Archive-663/lensAdapters/Olympus PEN-F/ASSETS/dumbAdapter_DKL_PENF (1).jpg

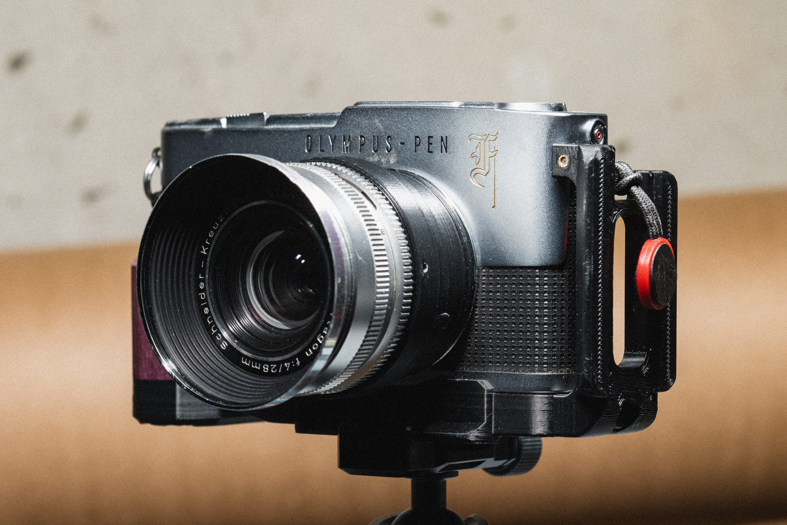
Olympus PEN-F/ASSETS/dumbAdapter_DKL_PENF (1).jpg
