Archive-663/lensAdapters/Olympus PEN-F/ASSETS/dumbAdapter_PENF.jpg

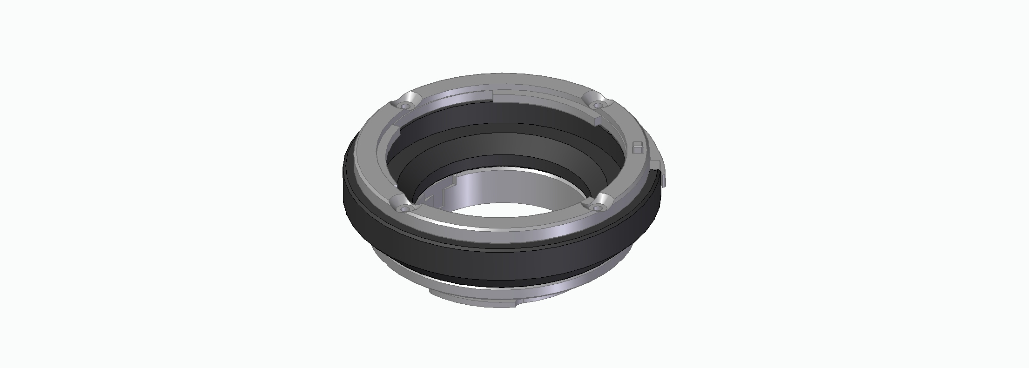
Olympus PEN-F/ASSETS/dumbAdapter_PENF.jpg
