Archive-663/lensAdapters/Olympus PEN-F/SHIFT/M42/ASSETS/productShift_M43_PENF (1).jpg

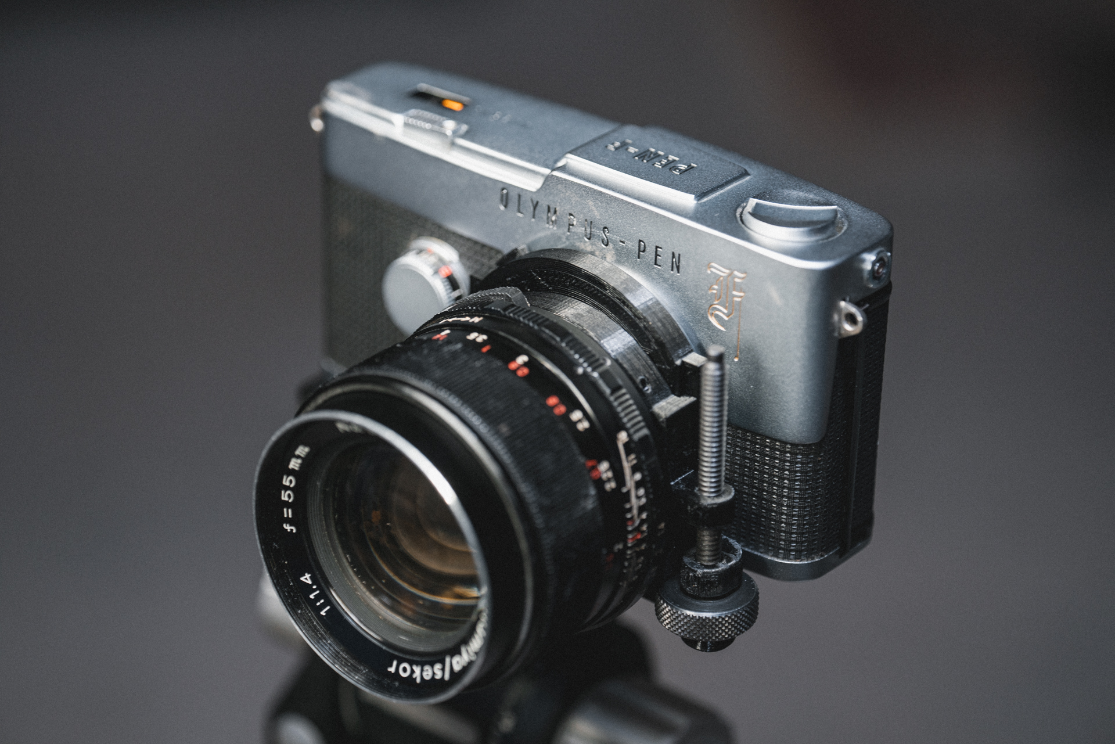
Olympus PEN-F/SHIFT/M42/ASSETS/productShift_M43_PENF (1).jpg
