Archive-663/lensAdapters/Olympus PEN-F/SHIFT/M42/ASSETS/productShift_M43_PENF (9).jpg

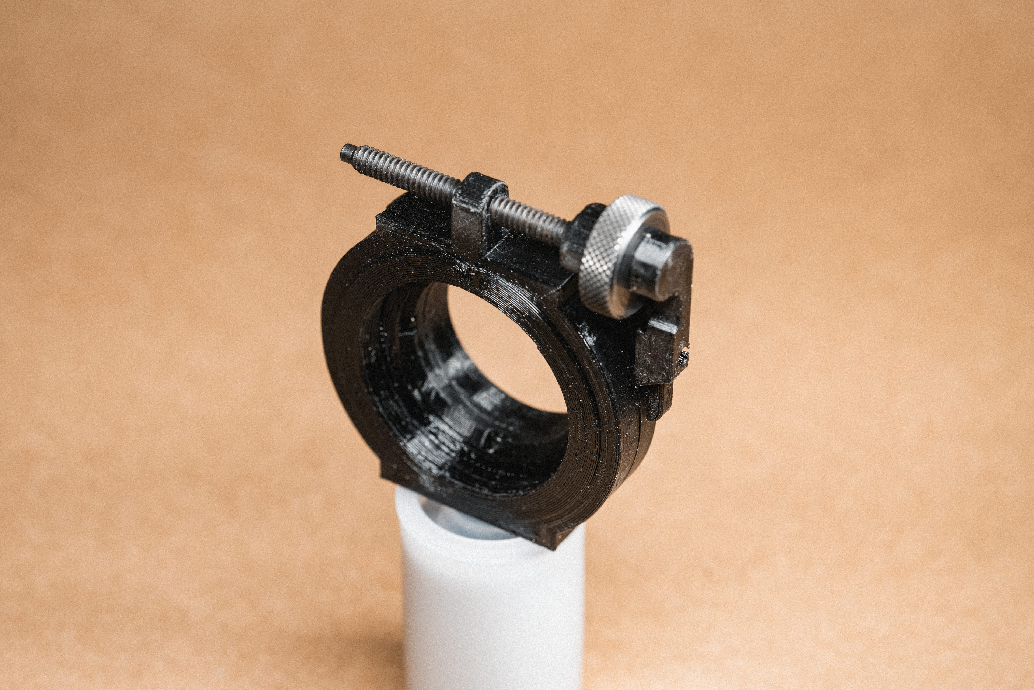
Olympus PEN-F/SHIFT/M42/ASSETS/productShift_M43_PENF (9).jpg
