Archive-663/lensAdapters/Olympus PEN-F/SHIFT/Nikon F/ASSETS/productShift_NIKF_PENF (7).jpg

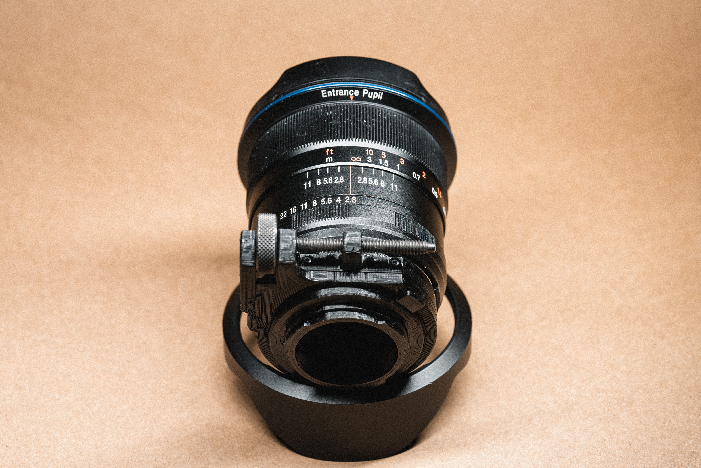
Olympus PEN-F/SHIFT/Nikon F/ASSETS/productShift_NIKF_PENF (7).jpg
