Archive-663/lensAdapters/Olympus PEN-F/SPEEDBOOSTER/Mamiya 645/ASSETS/productSB_M645_PENF (6).jpg

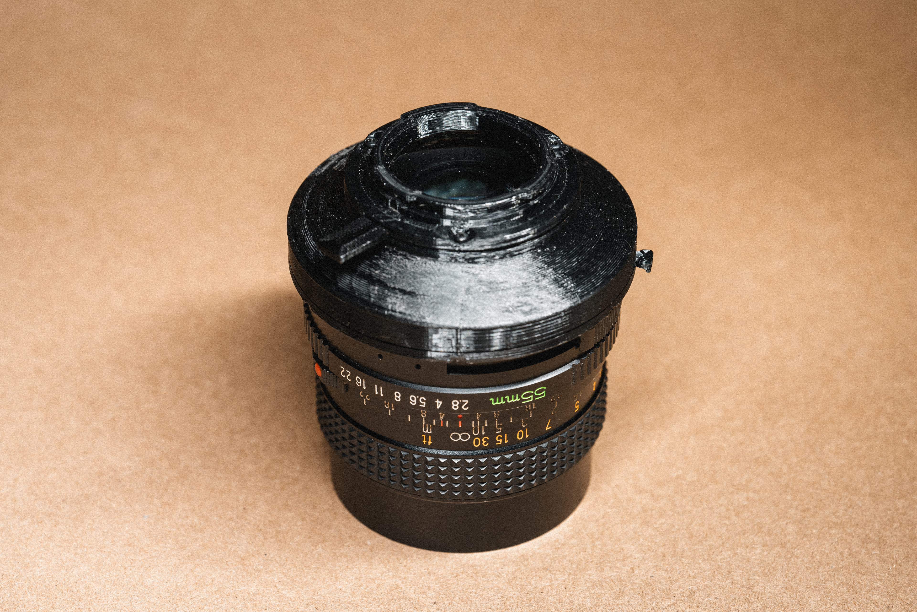
Olympus PEN-F/SPEEDBOOSTER/Mamiya 645/ASSETS/productSB_M645_PENF (6).jpg
