Archive-663/lensAdapters/Olympus PEN-F/DUMB/Canon FD/STEP/dumbBody_CFD_PENF.stp

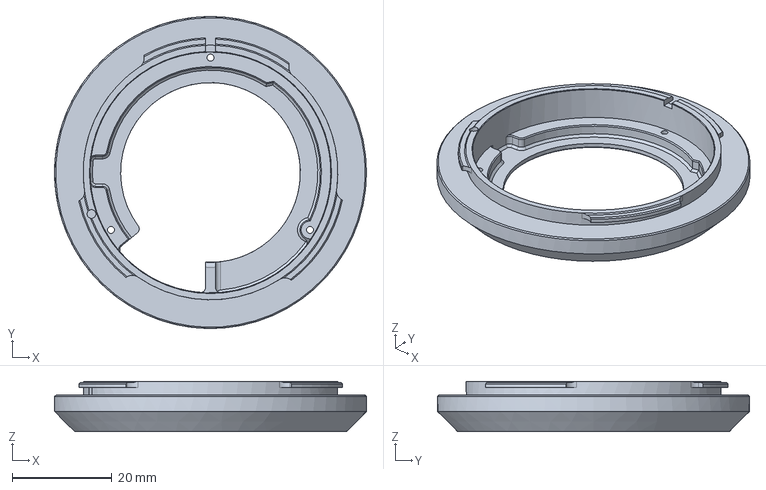
[picture p47: CAD file, 2025-03-07]
Olympus PEN-F/DUMB/Canon FD/STEP/dumbBody_CFD_PENF.stp
62.5 x 62.5 x 10.1 mm
