Archive-663/lensAdapters/Olympus PEN-F/DUMB/Canon FD/STL/dumbBody_CFD_PENF_printOrientation.3mf

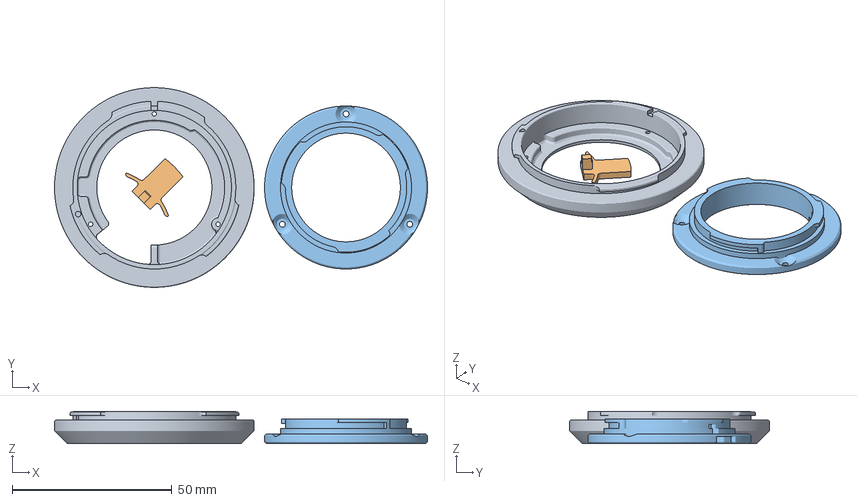
[picture p48: CAD file, 2025-03-07]
Olympus PEN-F/DUMB/Canon FD/STL/dumbBody_CFD_PENF_printOrientation.3mf
116.7 x 62.5 x 10.1 mm
dumbBody_CFD_PENF.stl
mountLensBase_lensLock_extended_PENF.stl
mountLensDumbBody_CFD_PENF.stl
