Archive-663/lensAdapters/Olympus PEN-F/DUMB/DKL/STL/mountBodyApertureRing_DKL_stepless.stl

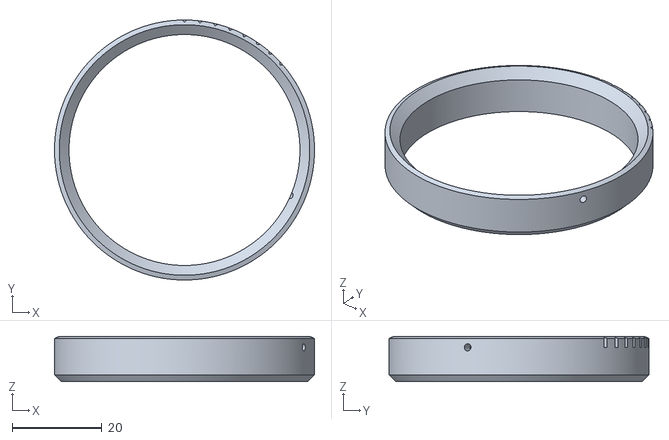
[picture p49: CAD file, 2023-10-16]
Olympus PEN-F/DUMB/DKL/STL/mountBodyApertureRing_DKL_stepless.stl
58.0 x 58.0 x 10.1
