Archive-663/lensAdapters/Olympus PEN-F/DUMB/M42/STL/printOrientation_baseDumbBody_M42_PENF.3mf

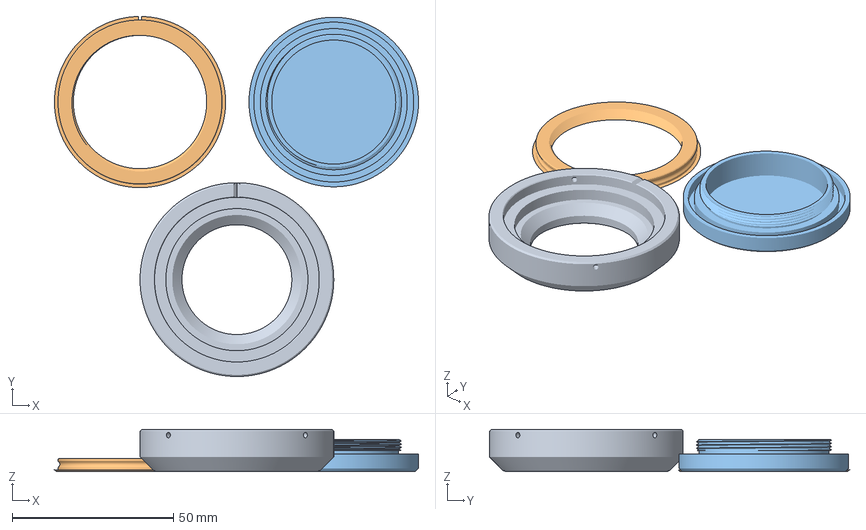
[picture p50: CAD file, 2023-09-29]
Olympus PEN-F/DUMB/M42/STL/printOrientation_baseDumbBody_M42_PENF.3mf
112.7 x 111.5 x 13.1 mm
dumbBody_M42_PENF.stl
mountBodyBaseThread_M42_PENF.stl
baseBodyCap_M42.stl
