Archive-663/lensAdapters/Olympus PEN-F/DUMB/mountDumbBase_PENF/STEP/mountLensLock_PENF.stp

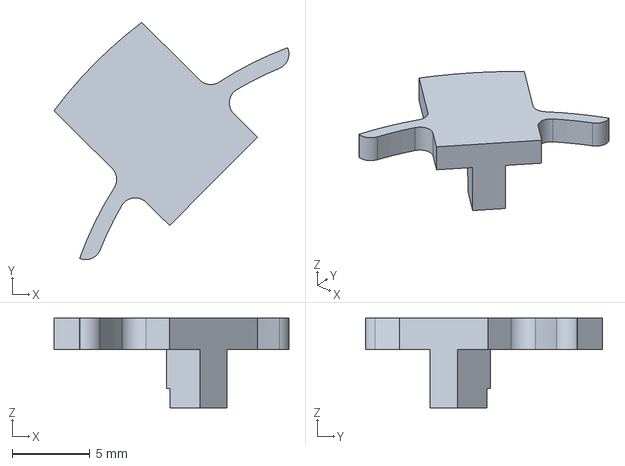
[picture p51: CAD file, 2023-09-29]
Olympus PEN-F/DUMB/mountDumbBase_PENF/STEP/mountLensLock_PENF.stp
15.1 x 15.2 x 5.75 mm
