Archive-663/lensAdapters/Olympus PEN-F/DUMB/mountDumbBase_PENF/STL/printOrientation_baseDumb_PENF.3mf

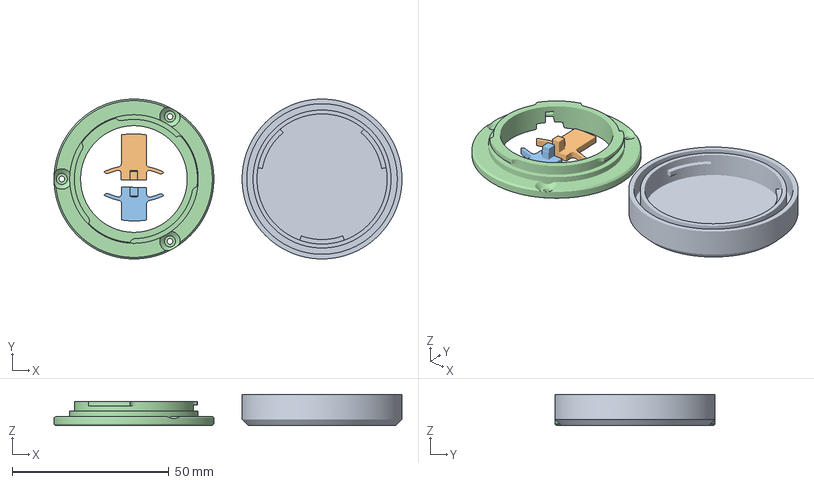
[picture p52: CAD file, 2023-09-29]
Olympus PEN-F/DUMB/mountDumbBase_PENF/STL/printOrientation_baseDumb_PENF.3mf
111.0 x 51.0 x 10.0 mm
baseRearCap_PENF.stl
mountLensLock_Extended_PENF.stl
mountLensLock_PENF.stl
mountLensBase_PENF.stl
