Archive-663/lensAdapters/Olympus PEN-F/DUMB/Nikon F/STL/printOrientation_baseDumbBody_NIKF_PENF.3mf

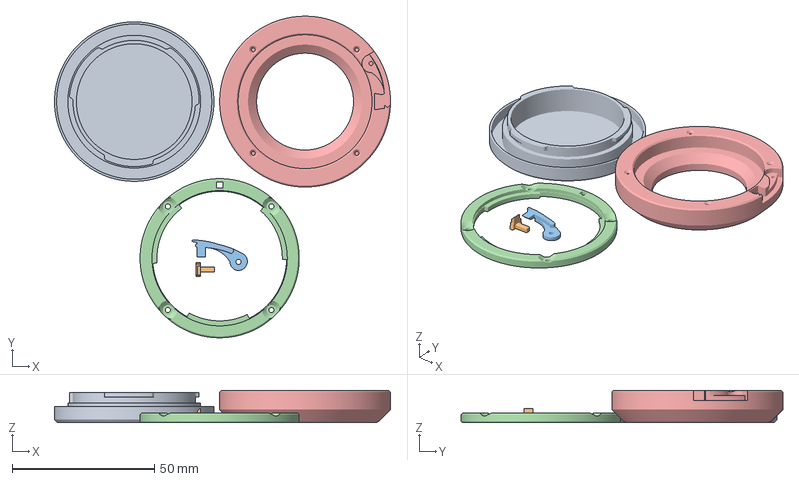
[picture p53: CAD file, 2023-09-29]
Olympus PEN-F/DUMB/Nikon F/STL/printOrientation_baseDumbBody_NIKF_PENF.3mf
118.0 x 112.9 x 11.3 mm
baseBodyCap_NIKF.stl
mountBodyPin_NIKF.stl
mountBodyPinLock_NIKF.stl
mountBodyBase_NIKF.stl
dumbBody_NIKF_PENF.stl
