Archive-663/lensAdapters/Olympus PEN-F/DUMB/Olympus OM/STL/dumbBody_OM_PENF_printOrientation.3mf

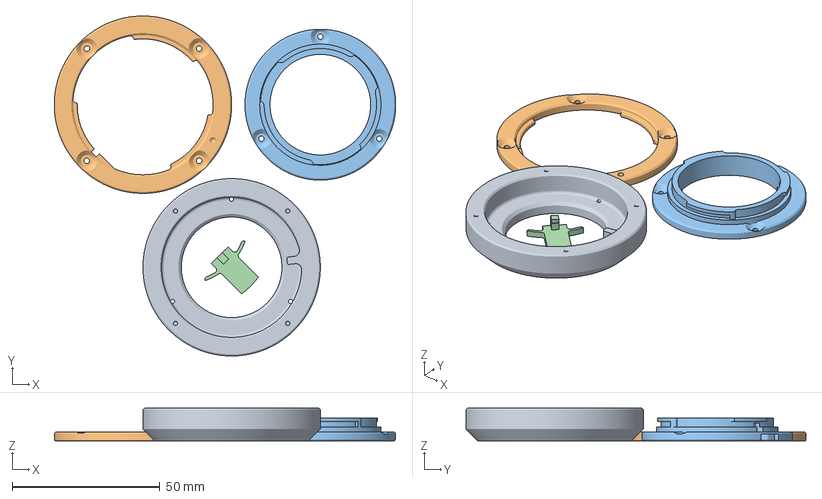
[picture p54: CAD file, 2025-08-07]
Olympus PEN-F/DUMB/Olympus OM/STL/dumbBody_OM_PENF_printOrientation.3mf
115.5 x 115.0 x 11.1 mm
dumbBody_OM_PENF.stl
dumbBodyFlange_OM_PENF.stl
mountLensDumbBody_PENF.stl
mountLensLock_Extended_PENF.stl
