Archive-663/lensAdapters/Olympus PEN-F/SHIFT/M42/STL/printOrientation_baseShiftBody_M42_PENF.3mf

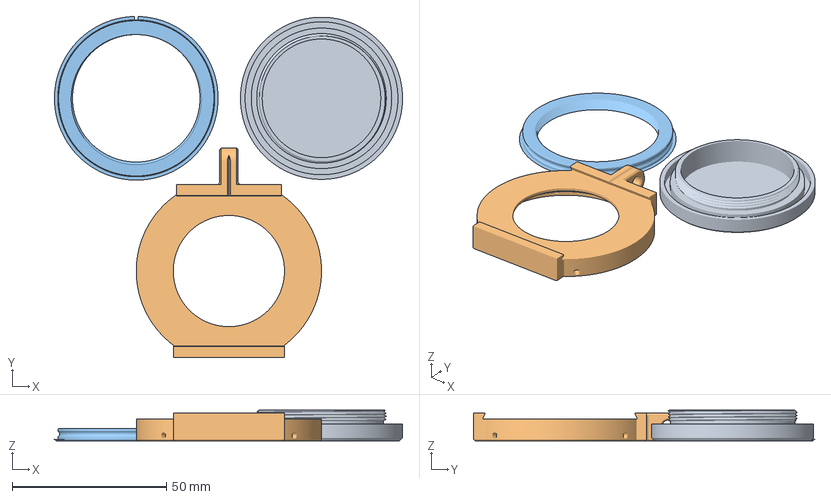
[picture p55: CAD file, 2023-09-29]
Olympus PEN-F/SHIFT/M42/STL/printOrientation_baseShiftBody_M42_PENF.3mf
112.7 x 110.4 x 10.0 mm
baseBodyCap_M42.stl
shiftTopPlate_M42_PENF.stl
mountBodyBaseThread_M42.stl
