Archive-663/lensAdapters/Olympus PEN-F/SHIFT/mountShiftBase_PENF/STL/printOrientation_baseShift_PENF.3mf

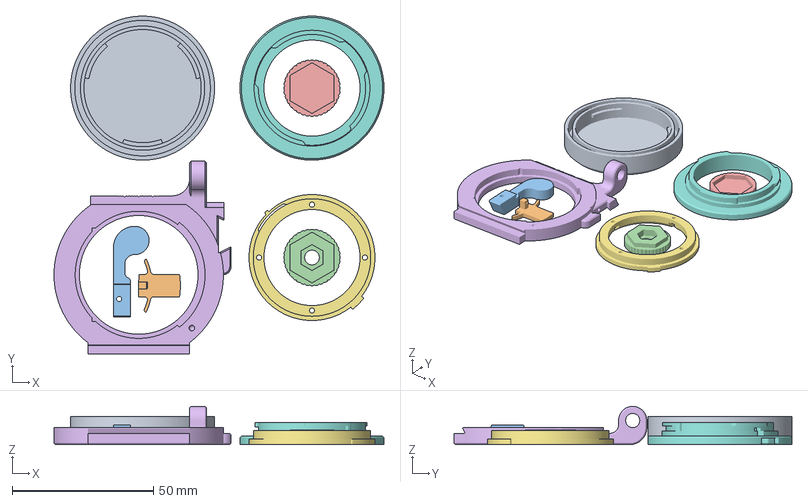
[picture p56: CAD file, 2023-09-29]
Olympus PEN-F/SHIFT/mountShiftBase_PENF/STL/printOrientation_baseShift_PENF.3mf
116.9 x 119.6 x 13.5 mm
baseRearCap_PENF.stl
shiftBaseMountLock_Extended_PENF.stl
shiftBaseBottomPlate_screwCap_PENF.stl
shiftBaseScrewCap_Bottom_PENF.stl
shiftBaseScrewCap_Top_PENF.stl
shiftBaseBottomPlate_PENF.stl
shiftBaseRotator_PENF.stl
shiftBaseMount_PENF.stl
