Archive-663/lensAdapters/Olympus PEN-F/SHIFT/Nikon F/STL/printOrientation_baseShiftBody_NIKF_PENF.3mf

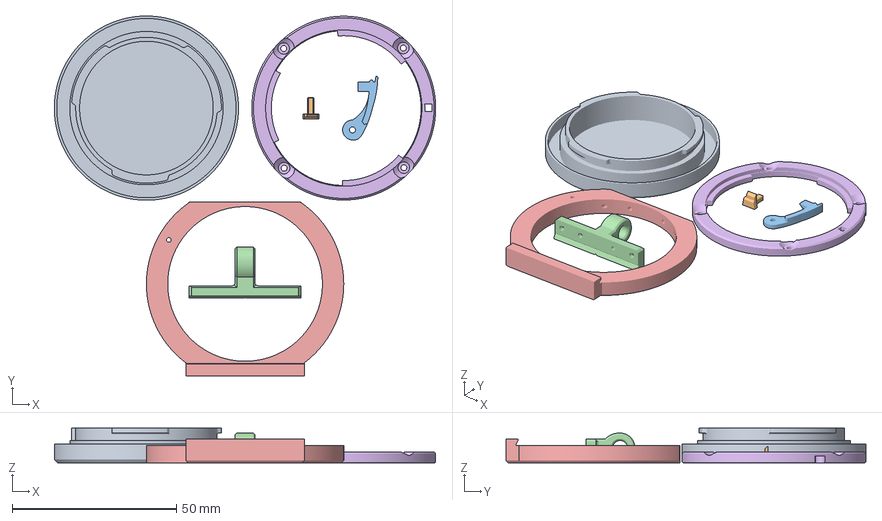
[picture p57: CAD file, 2023-09-29]
Olympus PEN-F/SHIFT/Nikon F/STL/printOrientation_baseShiftBody_NIKF_PENF.3mf
115.9 x 109.4 x 10.5 mm
baseBodyCap_NIKF.stl
mountBodyPin_NIKF.stl
mountBodyPinLock_NIKF.stl
shiftTopPlateShift_NIKF_PENF.stl
shiftTopPlate_NIKF_PENF.stl
mountBodyBase_NIKF.stl
