Archive-663/lensAdapters/Olympus PEN-F/SPEEDBOOSTER/Mamiya 645/STL/printOrientation_speedBooster_M645_PENF.3mf

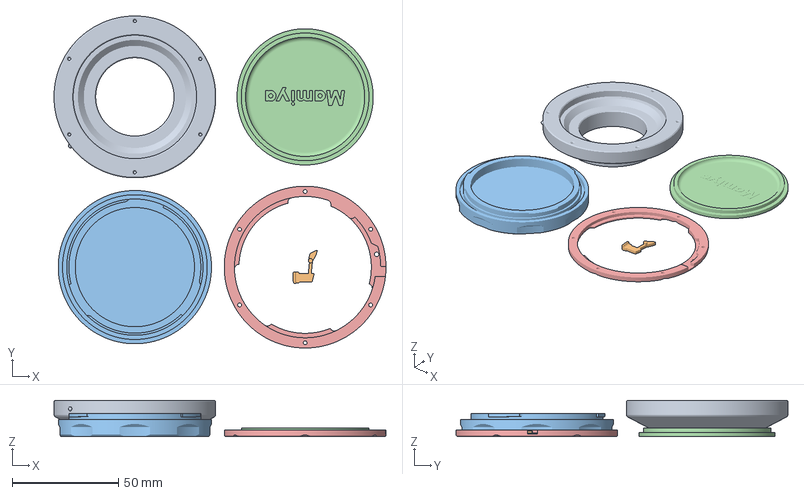
[picture p58: CAD file, 2023-09-29]
Olympus PEN-F/SPEEDBOOSTER/Mamiya 645/STL/printOrientation_speedBooster_M645_PENF.3mf
156.0 x 156.0 x 17.0 mm
speedBoosterBody_M645_PENF.stl
mountBodyLock_M645.stl
baseBodyCap_M645.stl
baseBodyCap_faceplate_M645.stl
mountBodyBase_M645.stl
