Archive-663/lensAdapters/Olympus PEN-F/SPEEDBOOSTER/mountSpeedBoosterBase_PENF/STEP/mountLensLock_Extended_PENF.stp

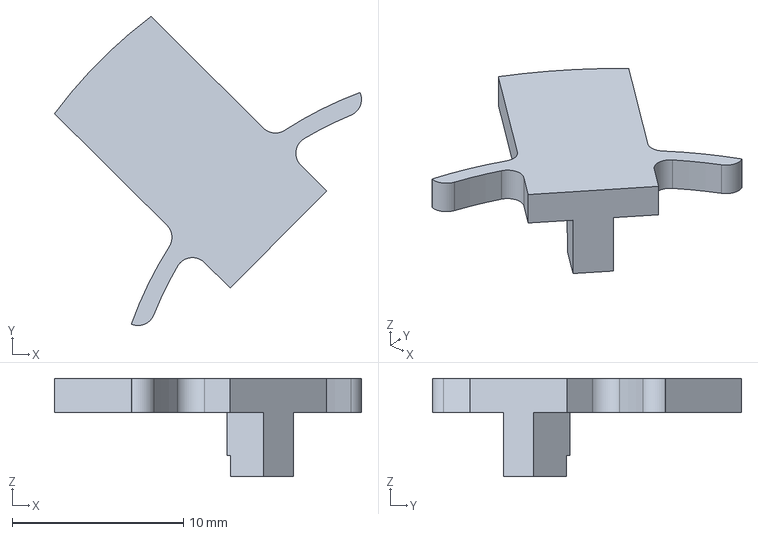
[picture p59: CAD file, 2023-09-29]
Olympus PEN-F/SPEEDBOOSTER/mountSpeedBoosterBase_PENF/STEP/mountLensLock_Extended_PENF.stp
17.9 x 18.1 x 5.75 mm
