Archive-663/lensAdapters/Canon EF-Mount/STEP/M42-EF EF Mount Body.step

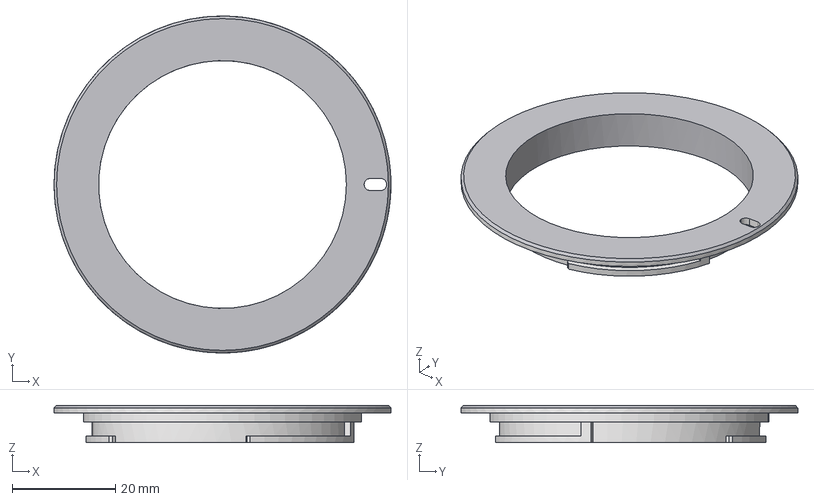
[picture p60: CAD file, 2023-06-25]
Canon EF-Mount/STEP/M42-EF EF Mount Body.step
65.3 x 65.3 x 7.21 mm
