Archive-663/lensAdapters/Fuji GFX/DUMB/Bronica S2/STEP/mountBodyBase_flange_BS_GFX.stp

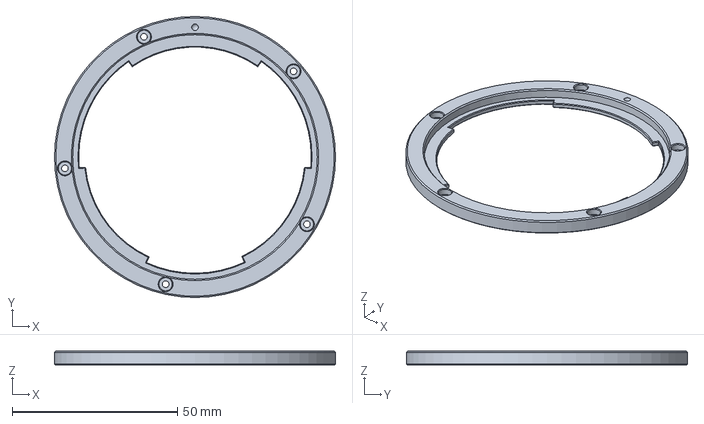
[picture p61: CAD file, 2026-01-14]
Fuji GFX/DUMB/Bronica S2/STEP/mountBodyBase_flange_BS_GFX.stp
85.0 x 85.0 x 4.25 mm
