Archive-663/lensAdapters/Fuji GFX/DUMB/Bronica S2/STL/dumbBody_BS_GFX_printOrientation.3mf

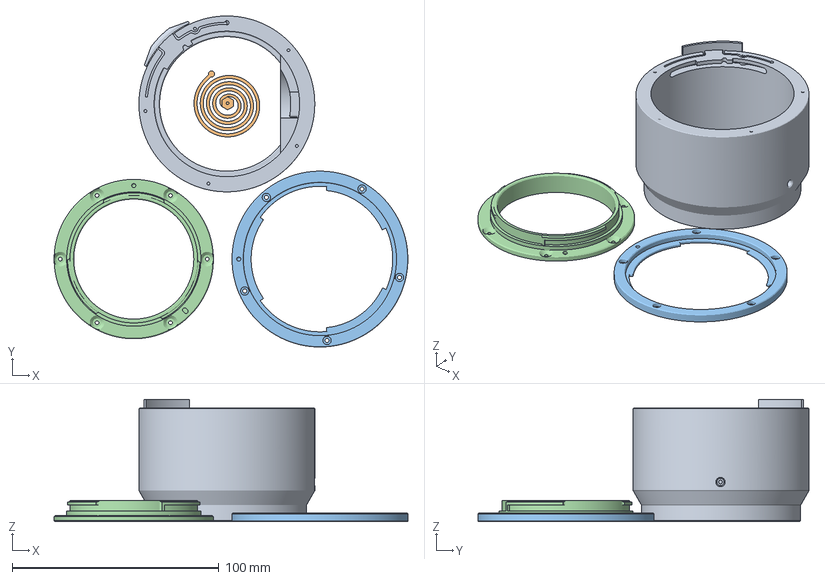
[picture p62: CAD file, 2026-01-14]
Fuji GFX/DUMB/Bronica S2/STL/dumbBody_BS_GFX_printOrientation.3mf
171.0 x 160.0 x 59.2 mm
dumbBody_BS_GFX.stl
mountBodyBase_apertureSpring_bronicaS2.stl
mountBodyBase_flange_bronicaS2.stl
mountLensBase_flange_GFX.stl
