Archive-663/lensAdapters/Olympus PEN-F/DUMB/Canon FD/STEP/mountLensDumbBody_CFD_PENF.stp

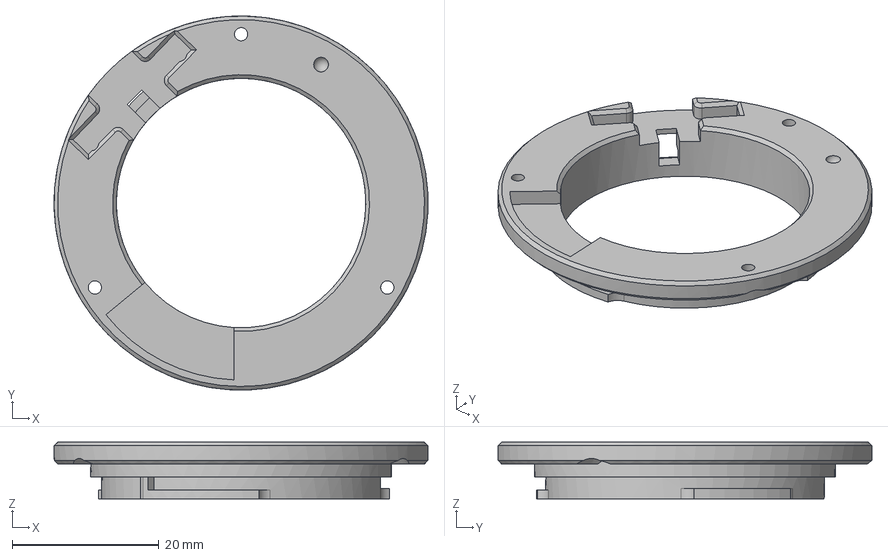
[picture p63: CAD file, 2025-03-07]
Olympus PEN-F/DUMB/Canon FD/STEP/mountLensDumbBody_CFD_PENF.stp
51.0 x 51.0 x 7.75 mm
