Archive-663/lensAdapters/Olympus PEN-F/DUMB/DKL/STL/mountBodyApertureRing_DKL.stl

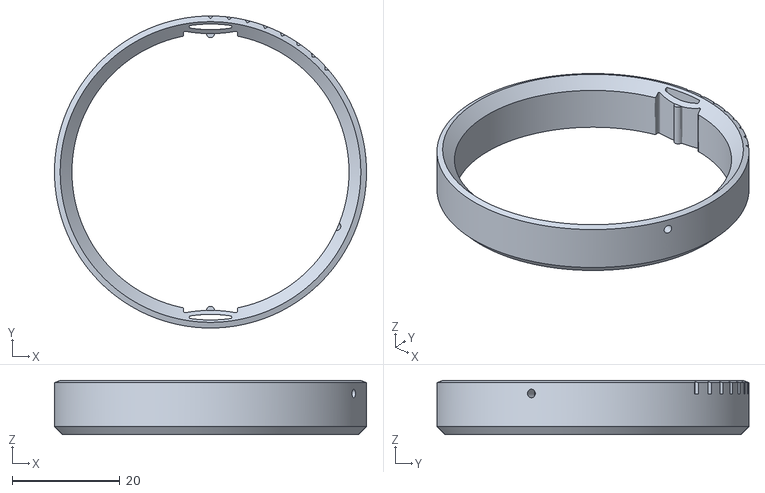
[picture p65: CAD file, 2023-10-16]
Olympus PEN-F/DUMB/DKL/STL/mountBodyApertureRing_DKL.stl
58.0 x 58.0 x 10.1
