Archive-663/lensAdapters/Olympus PEN-F/DUMB/M42/STEP/mountBodyBaseThread_M42.stp

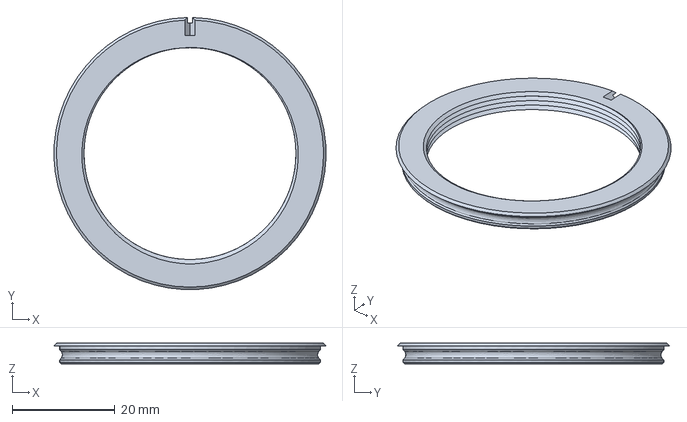
[picture p66: CAD file, 2023-09-29]
Olympus PEN-F/DUMB/M42/STEP/mountBodyBaseThread_M42.stp
53.0 x 53.0 x 4.00 mm
