Archive-663/lensAdapters/Olympus PEN-F/DUMB/Mamiya 645/STEP/baseBodyCap_M645.stp

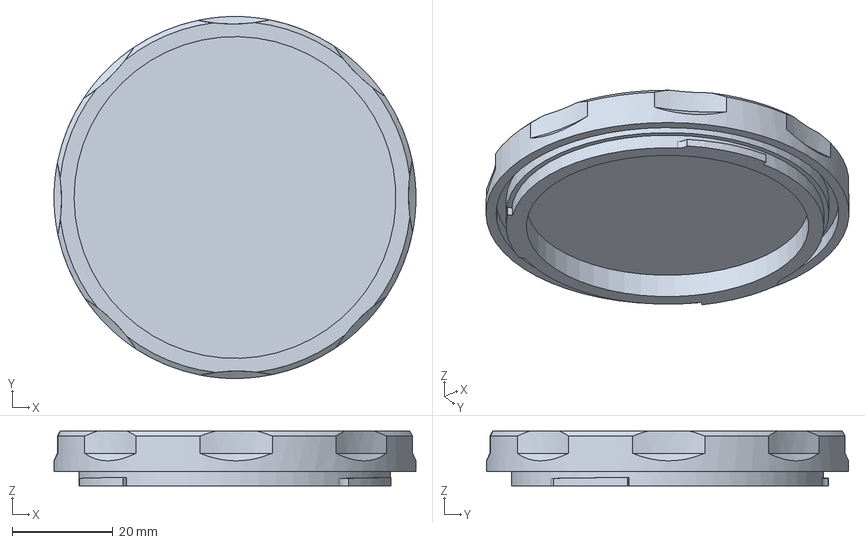
[picture p67: CAD file, 2023-09-29]
Olympus PEN-F/DUMB/Mamiya 645/STEP/baseBodyCap_M645.stp
72.0 x 72.0 x 10.9 mm
