Archive-663/lensAdapters/Olympus PEN-F/DUMB/mountDumbBase_PENF/STEP/mountLensBase_PENF.stp

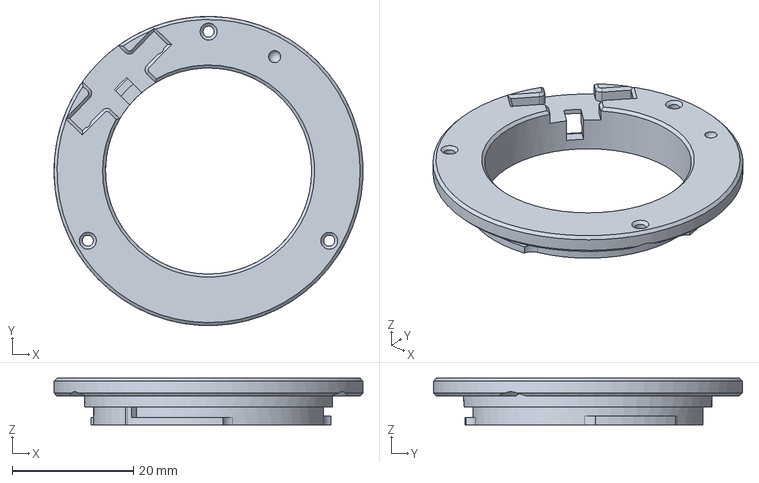
[picture p68: CAD file, 2023-09-29]
Olympus PEN-F/DUMB/mountDumbBase_PENF/STEP/mountLensBase_PENF.stp
51.0 x 51.0 x 7.75 mm
