Archive-663/lensAdapters/Olympus PEN-F/DUMB/Nikon F/STEP/mountBodyPinLock_NIKF.stp

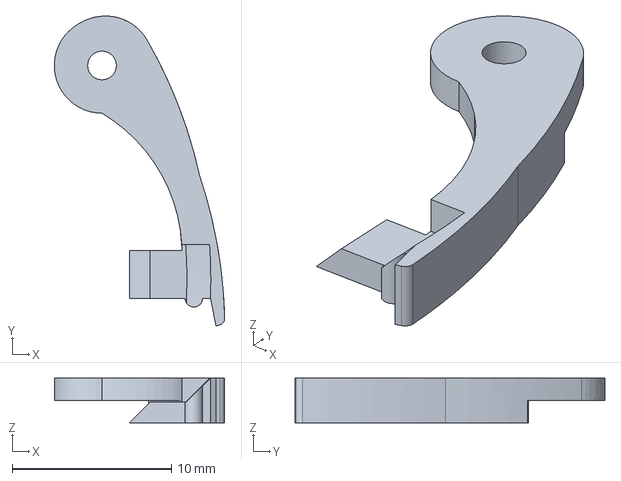
[picture p69: CAD file, 2023-09-29]
Olympus PEN-F/DUMB/Nikon F/STEP/mountBodyPinLock_NIKF.stp
10.7 x 19.5 x 2.80 mm
