Archive-663/lensAdapters/Olympus PEN-F/DUMB/Olympus OM/STEP/dumbBody_OM_PENF.stp

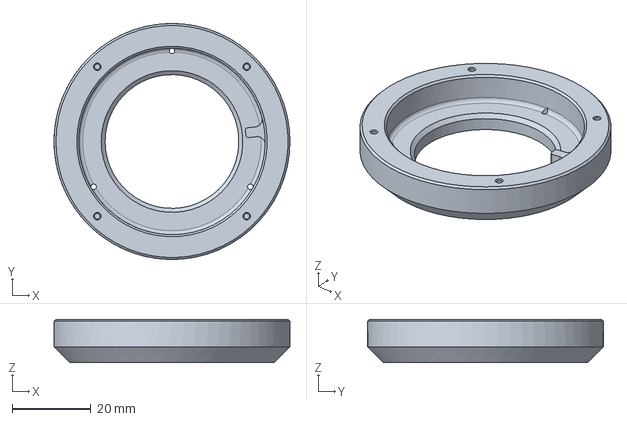
[picture p70: CAD file, 2025-08-07]
Olympus PEN-F/DUMB/Olympus OM/STEP/dumbBody_OM_PENF.stp
60.0 x 60.0 x 11.1 mm
