Archive-663/lensAdapters/Olympus PEN-F/SHIFT/M42/STEP/shiftTopPlate_M42_PENF.stp

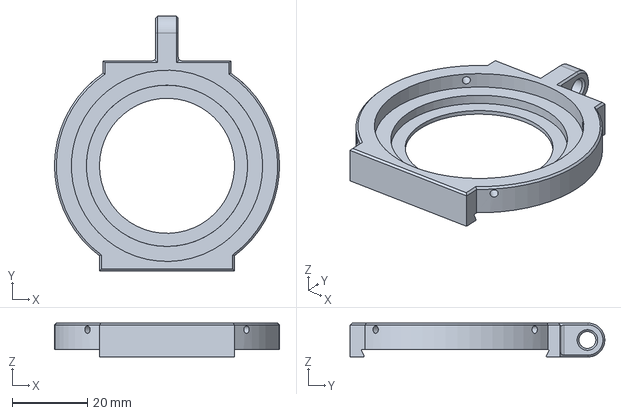
[picture p71: CAD file, 2023-09-29]
Olympus PEN-F/SHIFT/M42/STEP/shiftTopPlate_M42_PENF.stp
60.0 x 67.9 x 9.05 mm
