Archive-663/lensAdapters/Olympus PEN-F/SHIFT/Nikon F/STEP/mountBodyBase_NIKF.stp

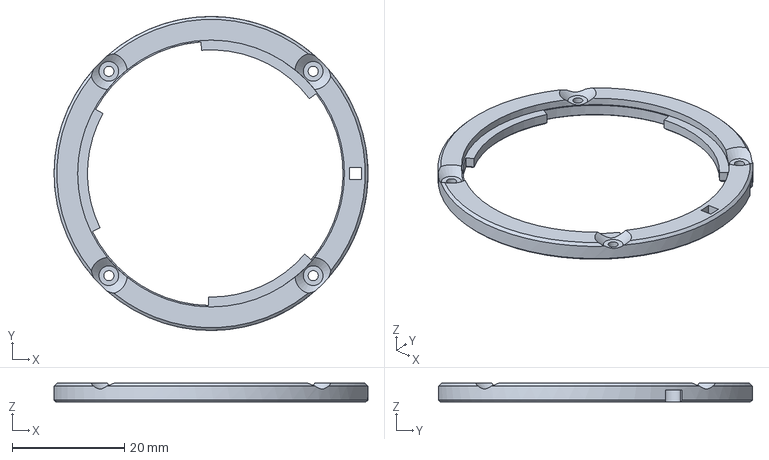
[picture p72: CAD file, 2023-09-29]
Olympus PEN-F/SHIFT/Nikon F/STEP/mountBodyBase_NIKF.stp
55.9 x 55.9 x 3.30 mm
