Archive-663/lensAdapters/Olympus PEN-F/SPEEDBOOSTER/Mamiya 645/STEP/mountBodyBase_M645.stp

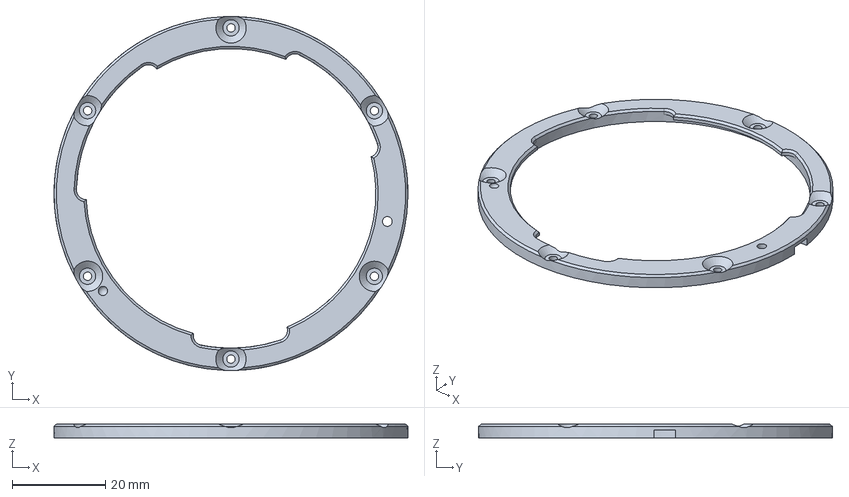
[picture p73: CAD file, 2023-09-29]
Olympus PEN-F/SPEEDBOOSTER/Mamiya 645/STEP/mountBodyBase_M645.stp
76.0 x 76.0 x 3.00 mm
