Archive-663/lensAdapters/Fuji GFX/DUMB/Bronica S2/STL/mountBodyBase_flange_bronicaS2.stl

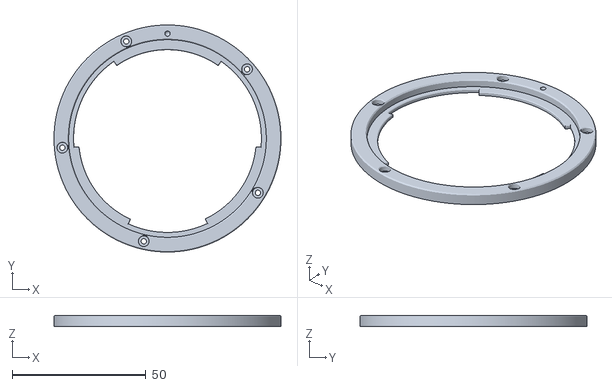
[picture p74: CAD file, 2026-01-14]
Fuji GFX/DUMB/Bronica S2/STL/mountBodyBase_flange_bronicaS2.stl
85.0 x 85.0 x 4.25
