Archive-663/lensAdapters/Olympus PEN-F/DUMB/DKL/STL/mountLensLock_DKL.stl

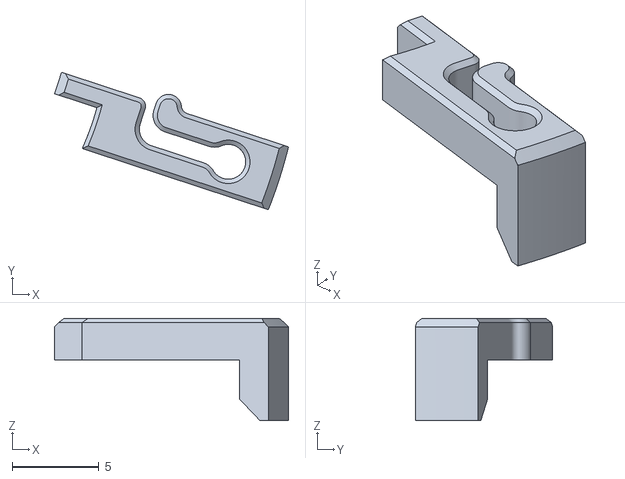
[picture p75: CAD file, 2023-10-16]
Olympus PEN-F/DUMB/DKL/STL/mountLensLock_DKL.stl
13.5 x 7.92 x 5.90
