Archive-663/lensAdapters/Olympus PEN-F/DUMB/M42/STEP/baseBodyCap_M42.stp

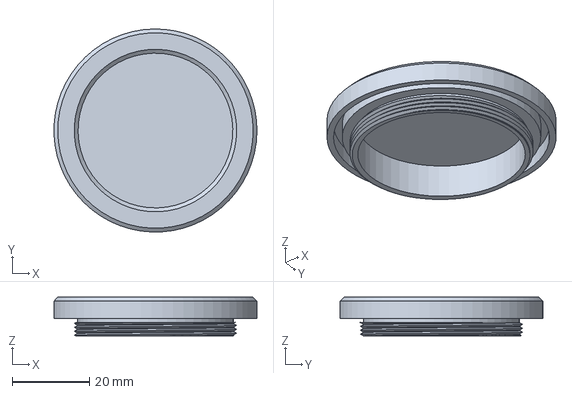
[picture p76: CAD file, 2023-09-29]
Olympus PEN-F/DUMB/M42/STEP/baseBodyCap_M42.stp
52.5 x 52.5 x 10.0 mm
