Archive-663/lensAdapters/Olympus PEN-F/DUMB/Mamiya 645/STEP/mountBodyLock_M645.stp

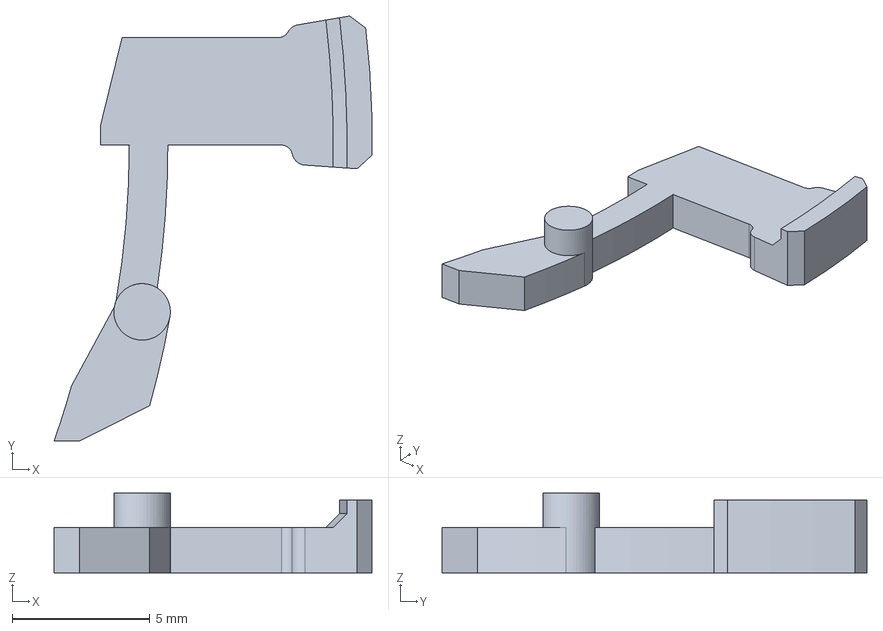
[picture p77: CAD file, 2023-09-29]
Olympus PEN-F/DUMB/Mamiya 645/STEP/mountBodyLock_M645.stp
11.5 x 15.4 x 2.90 mm
