Archive-663/lensAdapters/Olympus PEN-F/DUMB/mountDumbBase_PENF/STEP/baseRearCap_PENF.stp

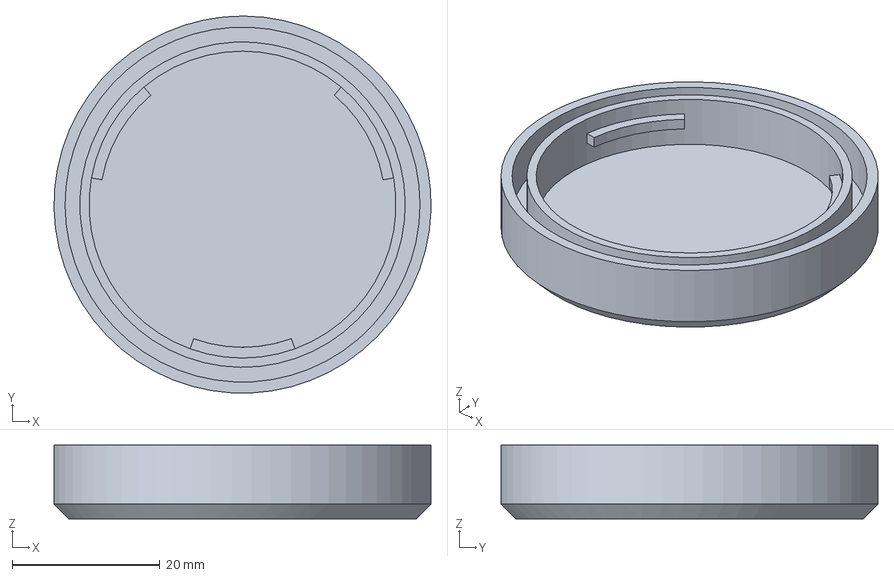
[picture p78: CAD file, 2023-09-29]
Olympus PEN-F/DUMB/mountDumbBase_PENF/STEP/baseRearCap_PENF.stp
51.0 x 51.0 x 10.0 mm
