Archive-663/lensAdapters/Olympus PEN-F/DUMB/Nikon F/STEP/dumbBody_NIKF_PENF.stp

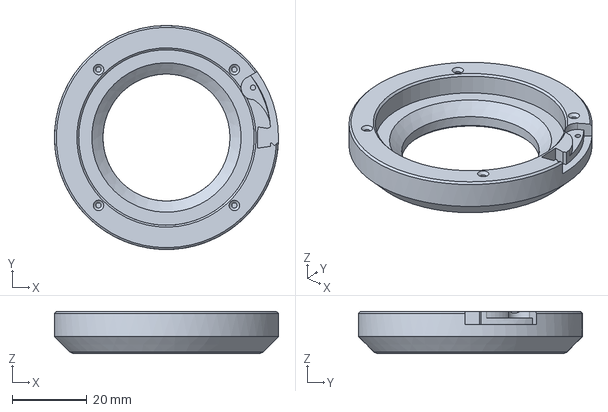
[picture p79: CAD file, 2023-09-29]
Olympus PEN-F/DUMB/Nikon F/STEP/dumbBody_NIKF_PENF.stp
60.0 x 60.0 x 11.2 mm
