Archive-663/lensAdapters/Olympus PEN-F/DUMB/Olympus OM/STEP/mountLensDumbBody_OM_PENF.stp

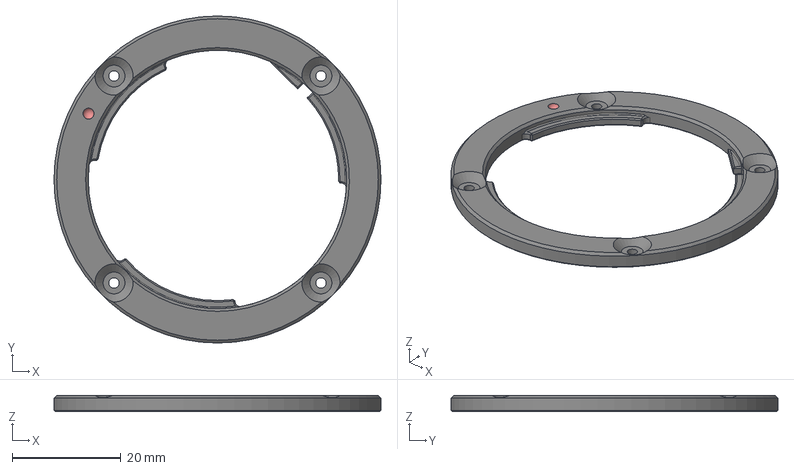
[picture p80: CAD file, 2025-08-07]
Olympus PEN-F/DUMB/Olympus OM/STEP/mountLensDumbBody_OM_PENF.stp
60.0 x 60.0 x 3.00 mm
