Archive-663/lensAdapters/Olympus PEN-F/SHIFT/Nikon F/STEP/shiftTopPlate_NIKF_PENF.stp

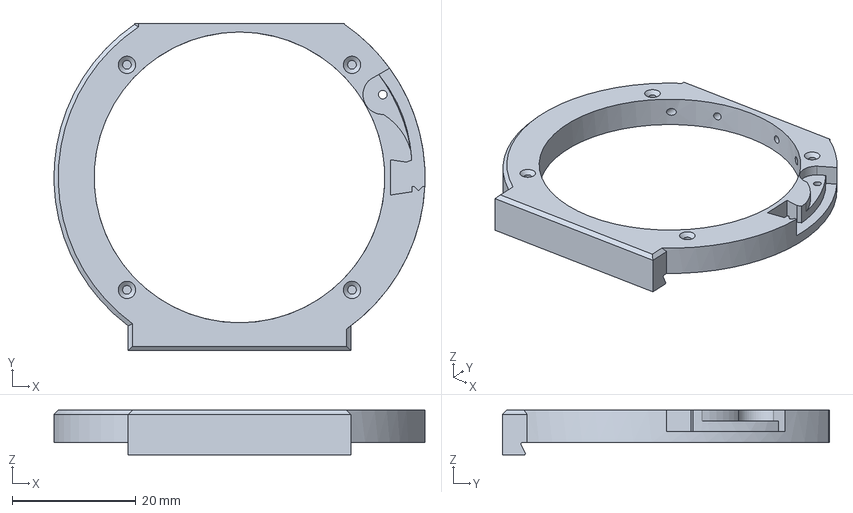
[picture p81: CAD file, 2023-09-29]
Olympus PEN-F/SHIFT/Nikon F/STEP/shiftTopPlate_NIKF_PENF.stp
60.0 x 52.9 x 7.25 mm
