Archive-663/lensAdapters/Olympus PEN-F/SPEEDBOOSTER/Mamiya 645/STEP/speedBoosterBody_M645_PENF.stp

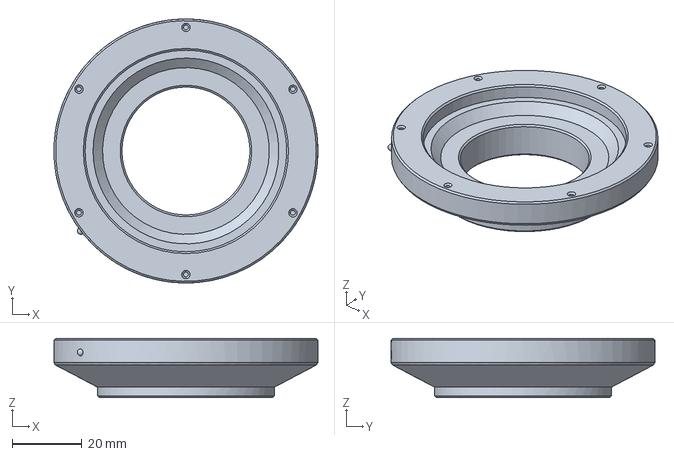
[picture p82: CAD file, 2023-09-29]
Olympus PEN-F/SPEEDBOOSTER/Mamiya 645/STEP/speedBoosterBody_M645_PENF.stp
76.0 x 76.0 x 17.0 mm
