Archive-663/lensAdapters/Fuji GFX/DUMB/Bronica S2/STEP/dumbBody_BS_GFX.stp

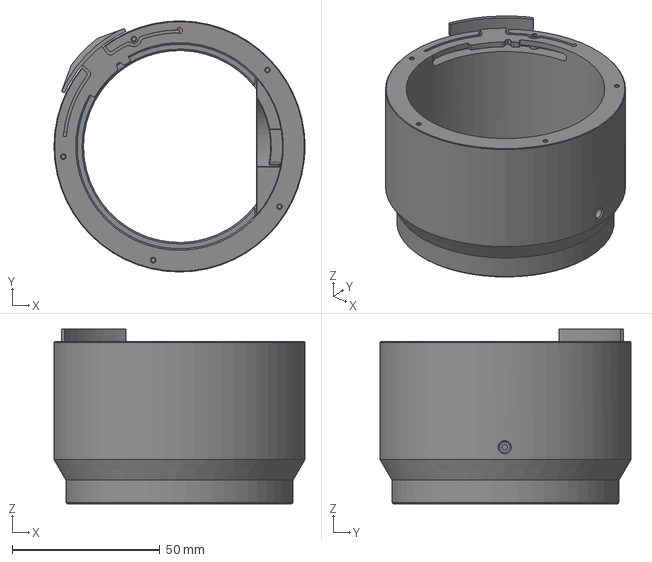
[picture p83: CAD file, 2026-01-14]
Fuji GFX/DUMB/Bronica S2/STEP/dumbBody_BS_GFX.stp
85.0 x 85.0 x 59.2 mm
