Archive-663/lensAdapters/Olympus PEN-F/DUMB/DKL/STEP/dumbBody_DKL_PENF.stp

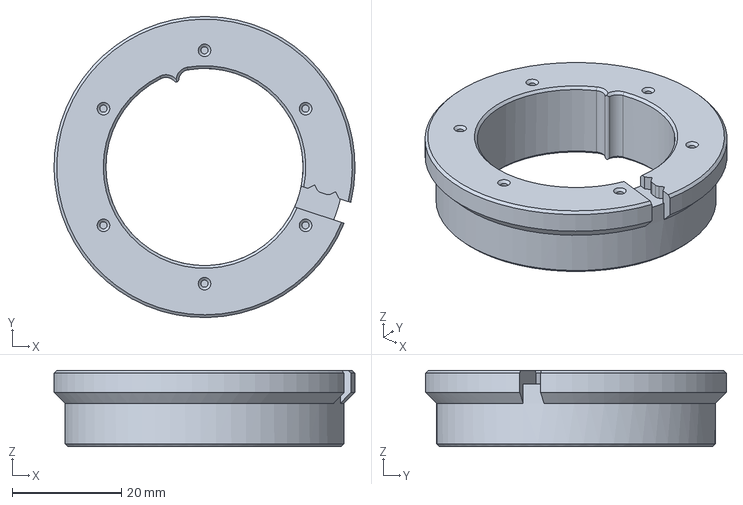
[picture p84: CAD file, 2023-12-12]
Olympus PEN-F/DUMB/DKL/STEP/dumbBody_DKL_PENF.stp
55.0 x 55.0 x 13.9 mm
