Archive-663/lensAdapters/Olympus PEN-F/DUMB/DKL/STL/printOrientation_baseDumbBody_DKL_PENF.3mf

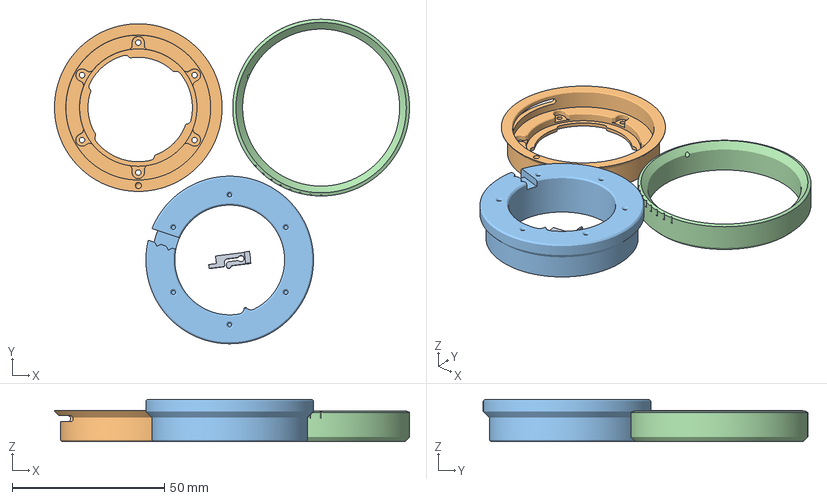
[picture p85: CAD file, 2023-10-16]
Olympus PEN-F/DUMB/DKL/STL/printOrientation_baseDumbBody_DKL_PENF.3mf
116.5 x 106.5 x 13.9 mm
mountLensLock_DKL.stl
mountBodyBase_DKL_stepless.stl
dumbBody_DKL_PENF.stl
mountBodyApertureRing_DKL_stepless.stl
