Archive-663/lensAdapters/Olympus PEN-F/DUMB/M42/STEP/dumbBody_M42_PENF.stp

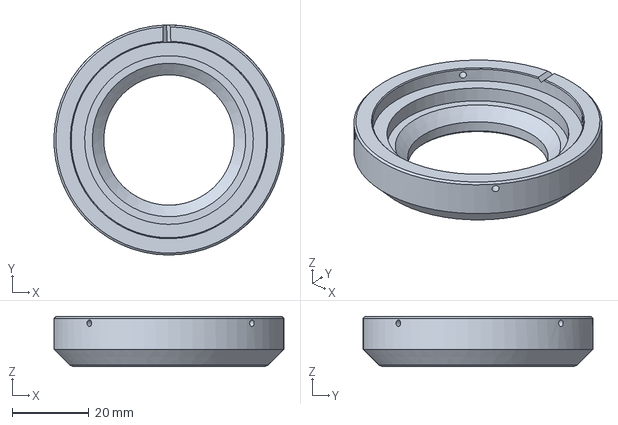
[picture p86: CAD file, 2023-09-29]
Olympus PEN-F/DUMB/M42/STEP/dumbBody_M42_PENF.stp
60.0 x 60.0 x 13.1 mm
