Archive-663/lensAdapters/Olympus PEN-F/DUMB/Mamiya 645/STEP/baseBodyCap_faceplate_M645.stp

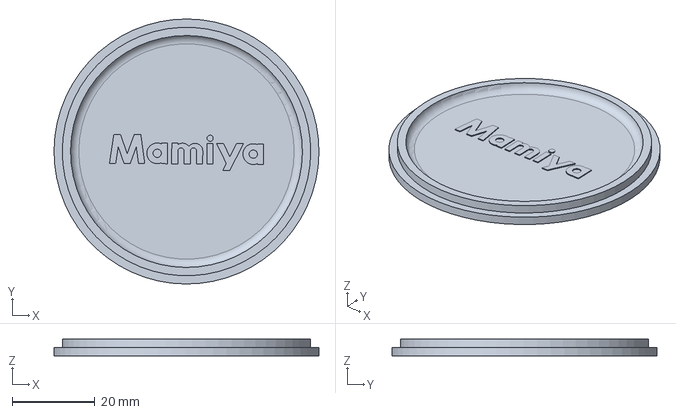
[picture p87: CAD file, 2023-09-29]
Olympus PEN-F/DUMB/Mamiya 645/STEP/baseBodyCap_faceplate_M645.stp
64.0 x 64.0 x 4.00 mm
