Archive-663/lensAdapters/Olympus PEN-F/SHIFT/Nikon F/STEP/mountBodyPin_NIKF.stp

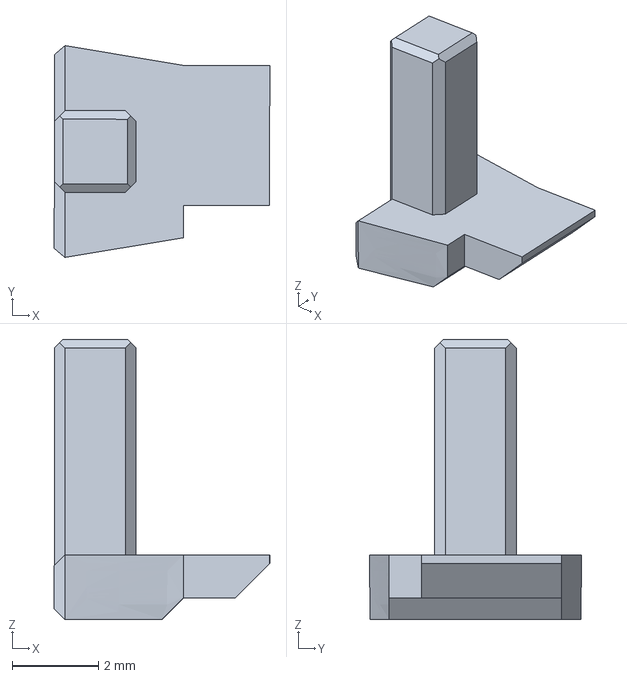
[picture p88: CAD file, 2023-09-29]
Olympus PEN-F/SHIFT/Nikon F/STEP/mountBodyPin_NIKF.stp
5.00 x 4.92 x 6.50 mm
