Archive-663/lensAdapters/Olympus PEN-F/DUMB/Mamiya 645/STEP/dumbBody_M645_PENF.stp

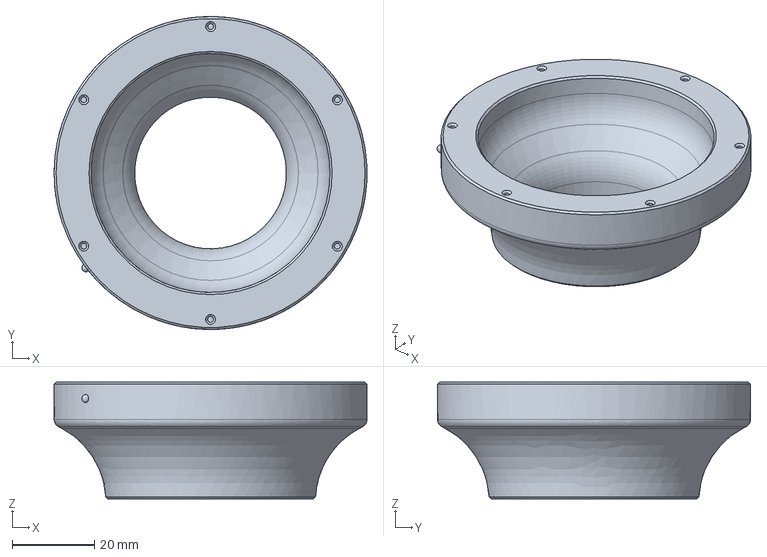
[picture p89: CAD file, 2023-09-29]
Olympus PEN-F/DUMB/Mamiya 645/STEP/dumbBody_M645_PENF.stp
76.0 x 76.0 x 28.4 mm
