Archive-663/lensAdapters/Olympus PEN-F/SHIFT/Nikon F/STEP/shiftTopPlateShift_NIKF_PENF.stp

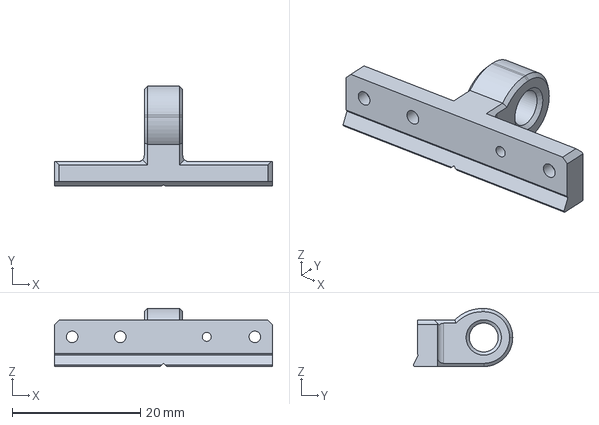
[picture p90: CAD file, 2023-09-29]
Olympus PEN-F/SHIFT/Nikon F/STEP/shiftTopPlateShift_NIKF_PENF.stp
34.0 x 15.5 x 9.05 mm
