Archive-663/lensAdapters/Olympus PEN-F/DUMB/Nikon F/STEP/baseBodyCap_NIKF.stp

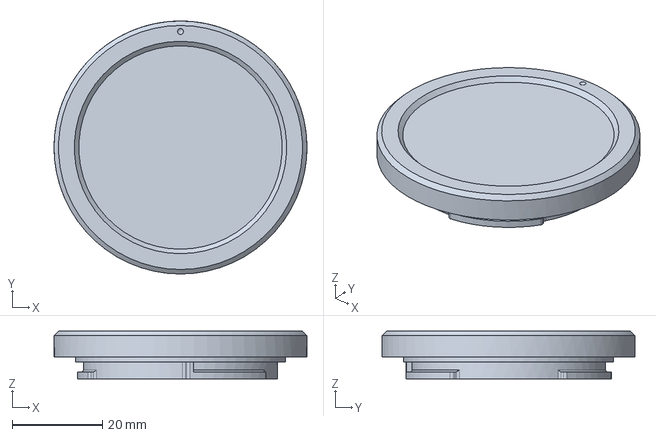
[picture p91: CAD file, 2023-09-29]
Olympus PEN-F/DUMB/Nikon F/STEP/baseBodyCap_NIKF.stp
56.0 x 56.0 x 10.5 mm
