Archive-663/lensAdapters/Olympus PEN-F/SHIFT/mountShiftBase_PENF/STEP/shiftBaseRotator_PENF.stp

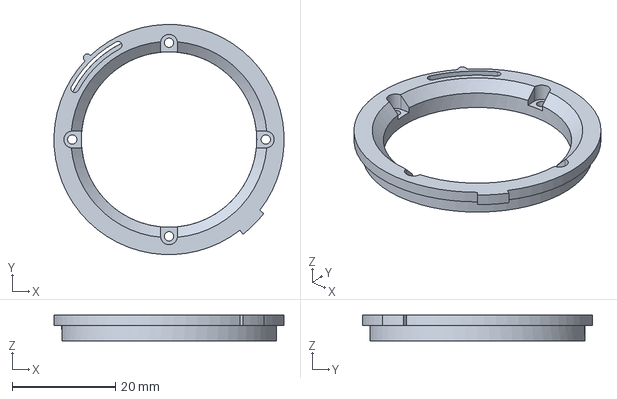
[picture p92: CAD file, 2023-09-29]
Olympus PEN-F/SHIFT/mountShiftBase_PENF/STEP/shiftBaseRotator_PENF.stp
44.6 x 44.6 x 5.00 mm
