Archive-663/lensAdapters/Olympus PEN-F/DUMB/DKL/STEP/mountBodyBase_DKL.stp

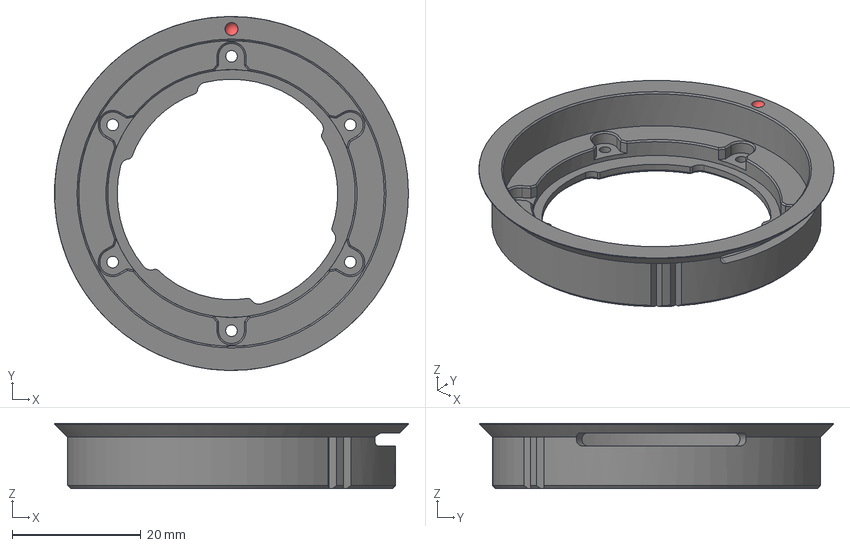
[picture p93: CAD file, 2023-12-12]
Olympus PEN-F/DUMB/DKL/STEP/mountBodyBase_DKL.stp
55.0 x 55.0 x 10.2 mm
