Archive-663/lensAdapters/Olympus PEN-F/SHIFT/mountShiftBase_PENF/STEP/shiftBaseBottomPlate_PENF.stp

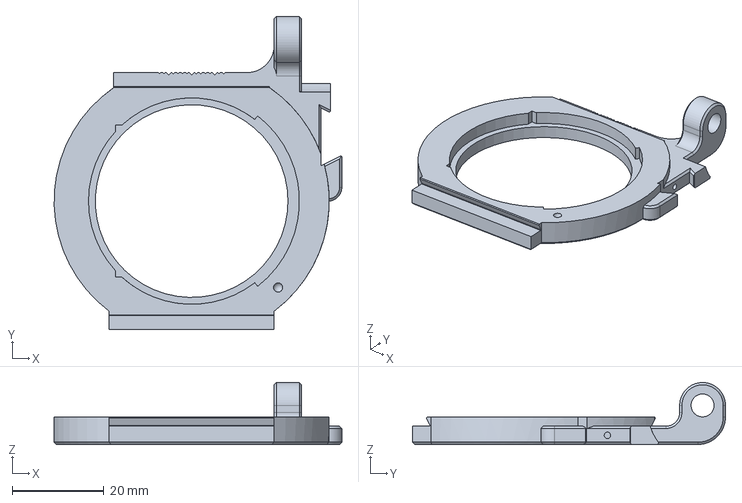
[picture p94: CAD file, 2023-09-29]
Olympus PEN-F/SHIFT/mountShiftBase_PENF/STEP/shiftBaseBottomPlate_PENF.stp
62.7 x 68.3 x 13.5 mm
